SoundCodes/8knobs/codes/octakhopar.ino

/*  
 *   Some blippy beats based off Reverb tank example
 modified by khoparzi
*/

#include <MozziGuts.h>
#include <ReverbTank.h>
#include <Oscil.h>
#include <tables/sin8192_int8.h>
#include <tables/cos8192_int8.h>
#include <tables/envelop2048_uint8.h>

ReverbTank reverb;

#define CONTROL_RATE 640 // quite fast, keeps modulation smooth

// Synth from PhaseMod_Envelope example
Oscil <COS8192_NUM_CELLS, AUDIO_RATE> aCarrier(COS8192_DATA);
Oscil <COS8192_NUM_CELLS, AUDIO_RATE> aModulator(COS8192_DATA);
Oscil <COS8192_NUM_CELLS, AUDIO_RATE> aModWidth(COS8192_DATA);
Oscil <SIN8192_NUM_CELLS, CONTROL_RATE> kModFreq1(SIN8192_DATA);
Oscil <COS8192_NUM_CELLS, CONTROL_RATE> kModFreq2(COS8192_DATA);
Oscil <ENVELOP2048_NUM_CELLS, AUDIO_RATE> aEnvelop(ENVELOP2048_DATA);


void setup(){
  // synth params
  aCarrier.setFreq(800);
  kModFreq1.setFreq(3.98f);
  kModFreq2.setFreq(3.31757f);
  aModWidth.setFreq(2.52434f);
  aEnvelop.setFreq(8.0f);

  startMozzi(CONTROL_RATE);
}


void updateControl(){
  // synth control
  // Base freq
  aCarrier.setFreq(mozziAnalogRead(A4)-mozziAnalogRead(A2)+100);
  // Mod
  kModFreq1.setFreq(mozziAnalogRead(A0)*0.0015625f);
  // High mod
  kModFreq2.setFreq(mozziAnalogRead(A1)*0.03125f);
  aModWidth.setFreq(mozziAnalogRead(A7)*0.001953125f);
  // Speed
  aEnvelop.setFreq((mozziAnalogRead(A4)-mozziAnalogRead(A3))*0.0078125f);
  aModulator.setFreq(277.0f + 0.4313f*kModFreq1.next() + kModFreq2.next());
}


int updateAudio(){
  int synth = aCarrier.phMod((int)aModulator.next()*(150u+aModWidth.next()));
  synth *= (byte)aEnvelop.next();
  synth >>= 8;
  // here's the reverb
  int arev = reverb.next(synth);
  // add the dry and wet signals
  return synth + (arev>>2);
}


void loop(){
  audioHook();
}
